prilosac/PriloRectangleController/src/chassis/old/3_SwitchPlate.dxf

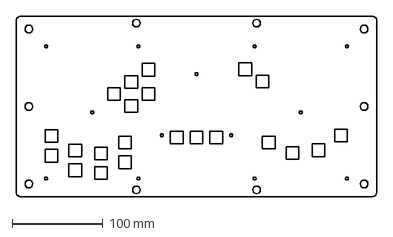
[picture p16: CAD file, 2022-11-01, an earlier design]
src/chassis/old/3_SwitchPlate.dxf
397.2 x 198.6 mm
