prilosac/PriloRectangleController/src/chassis/old/4_GCCMXCover.dxf

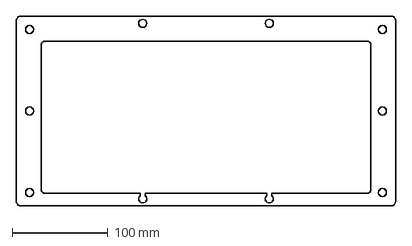
[picture p17: CAD file, 2022-11-01, an earlier design]
src/chassis/old/4_GCCMXCover.dxf
397.2 x 198.6 mm
