prilosac/PriloRectangleController/src/chassis/old/5_ModelSCover.dxf

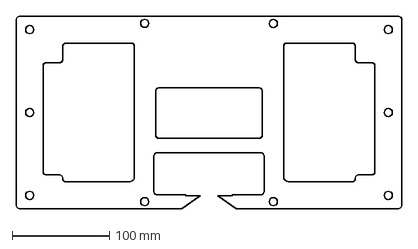
[picture p18: CAD file, 2022-11-01, an earlier design]
src/chassis/old/5_ModelSCover.dxf
397.2 x 198.6 mm
